Springwald/iGoBot/Python/hardware/GripperAndDispenser.py

#!/usr/bin/env python

#     ########################
#     # gripper servo module #
#     ########################
#
#     Licensed under MIT License (MIT)
#
#     Copyright (c) 2018 Daniel Springwald | daniel@springwald.de
#
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
from __future__ import division
import time, sys, os

import atexit

my_file = os.path.abspath(__file__)
my_path ='/'.join(my_file.split('/')[0:-1])

sys.path.insert(0,my_path + "/../libs" )
sys.path.insert(0,my_path + "/../DanielsRasPiPythonLibs" )
sys.path.insert(0,my_path + "/../DanielsRasPiPythonLibs/multitasking" )

from array import array
import Adafruit_PCA9685
import grovepi

from SharedInts import SharedInts
from SharedFloats import SharedFloats

class GripperAndDispenser():
	
	_groveRelaisPort = 7;
	
	_pwm		= None
	_released 	= False
	
	_servoCount = 2;

	_gripperOpen	= 340
	_gripperClosed	= 200
	
	_dispenserGive	= 285;
	_dispenserGrab	= 530;
	
	__last_servo_set_time = 0;
	
	allTargetsReached = False;
	
	_actualSpeedDelay = 0.01
	_maxStepsPerSecond = 390
	
	_name 		= "gripperAndDispenser"
	
	_targets 					= [0,0]
	_values						= [0.0,0.0]

	
	def __init__(self, i2cAdress, busnum):

		self.__last_servo_set_time = 0

		# Initialise the PCA9685 using the default address (0x40).
		#self._pwm = Adafruit_PCA9685.PCA9685()
		# Alternatively specify a different address and/or bus:
		self._pwm = Adafruit_PCA9685.PCA9685(address=i2cAdress, busnum=busnum)
		
		grovepi.pinMode(self._groveRelaisPort, "OUTPUT")
		
		self.PowerOn();
		
		# Set frequency to 60hz, good for servos.
		self._pwm.set_pwm_freq(60)
		
		# reset servo
		self._targets[0] = int(self._gripperOpen);
		self._values[0] = int(self._gripperOpen);
		self.setServo(0, int(self._gripperOpen))
		
		self._targets[1] = int(self._dispenserGive);
		self._values[1] = int(self._dispenserGive);
		self.setServo(1, int(self._dispenserGive))		
	
		
	def Update(self):
		
		allReached = True
		maxSpeed = self._maxStepsPerSecond * self._actualSpeedDelay;
		#print(maxSpeed)
		for i in range(0,self._servoCount):
			reachedThis = True
			diff = int(self._targets[i] - self._values[i])
			plus = 0
			if (diff > 0):
				plus = max(0.1, min(diff , maxSpeed))
				reachedThis = False
			if (diff < 0):
				plus = min(-0.1, max(diff , -maxSpeed))
				reachedThis = False
			if (reachedThis == False):
				allReached = False
				newValue = self._values[i] + plus
				self._values[i] = newValue;
				self.setServo(i,newValue)
				
		self.allTargetsReached = allReached

		if (allReached == False):
			#self.PowerOn();
			time.sleep(self._actualSpeedDelay);
		
		if (self.__last_servo_set_time + 1 < time.time()):
			# long time nothing done
			#time.sleep(0.5);
			self.PowerOff();
		
		#print("update end")

	def openGripper(self):
		self._targets[0] = self._gripperOpen;
		self.PowerOn();
		self.allTargetsReached = False

	def closeGripper(self):
		self._targets[0] = self._gripperClosed;
		self.PowerOn();
		self.allTargetsReached = False
		
	def dispenserGive(self):
		self._targets[1] = self._dispenserGive;
		self.PowerOn();
		self.allTargetsReached = False

	def dispenserGrab(self):
		self._targets[1] = self._dispenserGrab;
		self.PowerOn();
		self.allTargetsReached = False

	def setServo(self, port, value):
		self._pwm.set_pwm(port, 0, int(value))
		self.__last_servo_set_time = time.time()
		#self.power_on()
		
	def portDemo(self, port):
		self.setServo(port,0)
		self.allTargetsReached = False
		time.sleep(1)
		self.setServo(port,100)
		self.allTargetsReached = False
		time.sleep(1)
		self.setServo(port, int(self._handArmHomeValues[port]))
		self.allTargetsReached = False
		time.sleep(1)
		
	def PowerOn(self):
		grovepi.digitalWrite(self._groveRelaisPort,1)
		
	def PowerOff(self):
		grovepi.digitalWrite(self._groveRelaisPort,0)
		
	def turnOff(self):
		print("turning off " + self._name)
		self.PowerOff();

	def Release(self):
		if (self._released == False):
			print("releasing " + self._name)
			self.openGripper();
			self.dispenserGive();
			while(self.allTargetsReached == False):
				self.Update();
			self._released = True
			self.turnOff()

	def __del__(self):
		self.Release()
		
def exit_handler():
	tester.Release()

if __name__ == "__main__":
	
	#relais = RelaisI2C(I2cIoExpanderPcf8574(address=0x39, useAsInputs=False))
	
	tester = GripperAndDispenser(i2cAdress=0x40, busnum=1)

	atexit.register(exit_handler)
	
	time.sleep(1)
	
	for i in range(0,0):
		print(i)
		tester.dispenserGrab();
		while(tester.allTargetsReached == False):
			tester.Update();
		time.sleep(1)
		
		tester.dispenserGive();
		while(tester.allTargetsReached == False):
			tester.Update();
		time.sleep(1)
	
	tester.closeGripper();
	while(tester.allTargetsReached == False):
		tester.Update();
	time.sleep(4)
	
	tester.openGripper();
	while(tester.allTargetsReached == False):
		tester.Update();
	time.sleep(4)
